thejiral/Separator-filtration_system/images/magnetholder-heatinserts-front.png

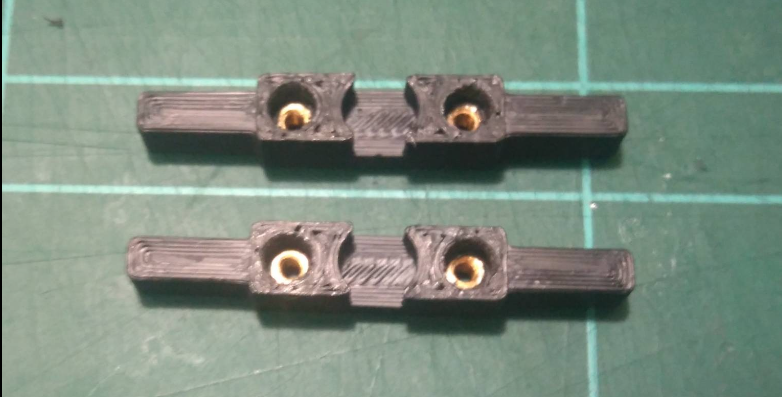
images/magnetholder-heatinserts-front.png
