thejiral/Separator-filtration_system/images/magnetholder-heatinserts.png

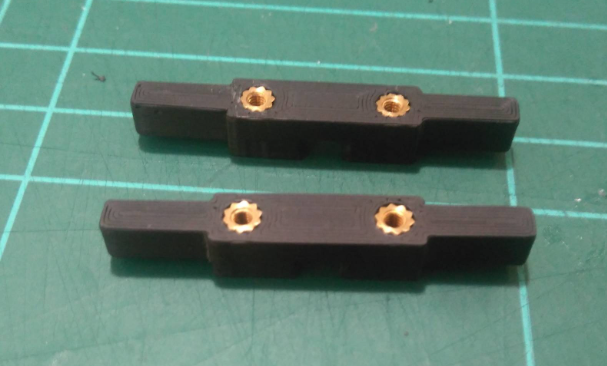
images/magnetholder-heatinserts.png
