thejiral/Separator-filtration_system/images/Meshinsert.png

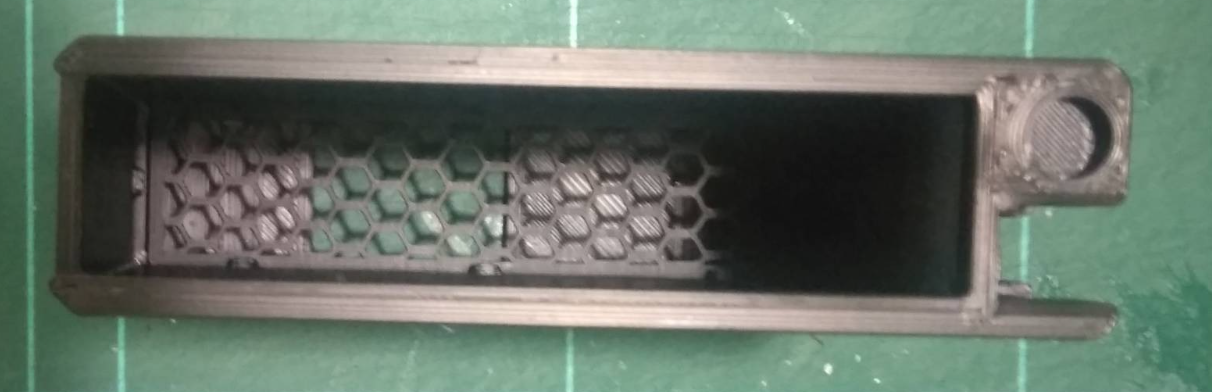
images/Meshinsert.png
