thejiral/Separator-filtration_system/images/PartA-heatinserts.png

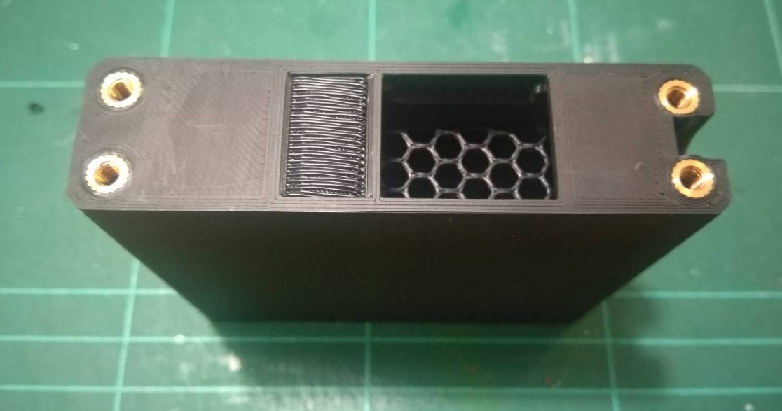
images/PartA-heatinserts.png
