thejiral/Separator-filtration_system/images/PartB-microfit_orientation.png

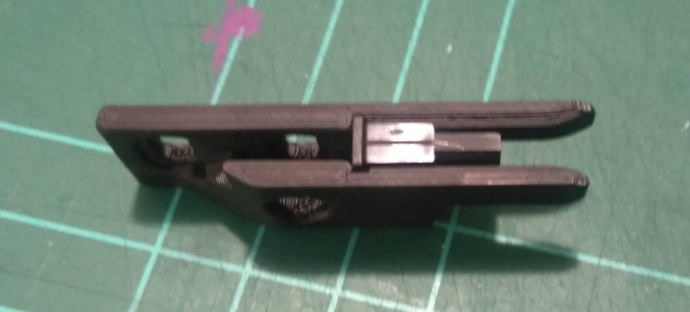
images/PartB-microfit_orientation.png
