thejiral/Separator-filtration_system/images/PartD+blower+cablemanagement.png

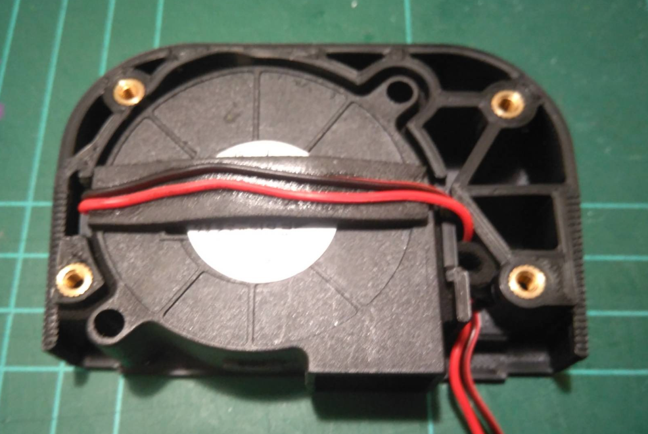
images/PartD+blower+cablemanagement.png
