thejiral/Separator-filtration_system/images/partD-heatinserts+EPDM.png

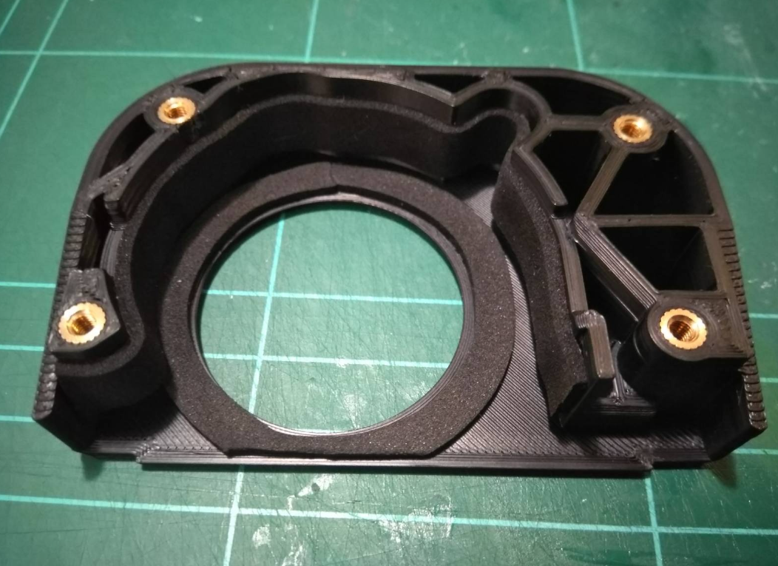
images/partD-heatinserts+EPDM.png
