thejiral/Separator-filtration_system/images/profile-magnet0.png

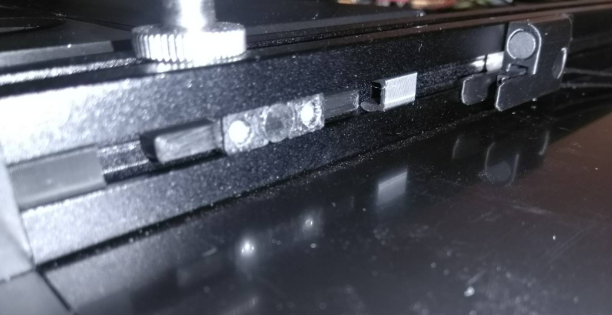
images/profile-magnet0.png
