thejiral/Separator-filtration_system/images/profile-magnet1.png

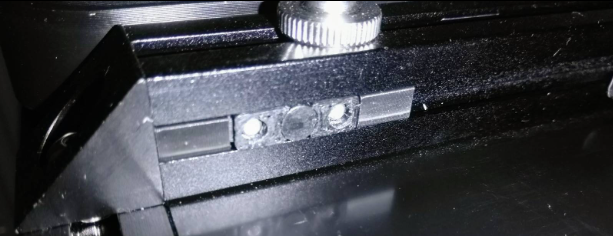
images/profile-magnet1.png
