thejiral/Separator-filtration_system/STL-dual_module/Separator-Mesh-front-modifier1.stl

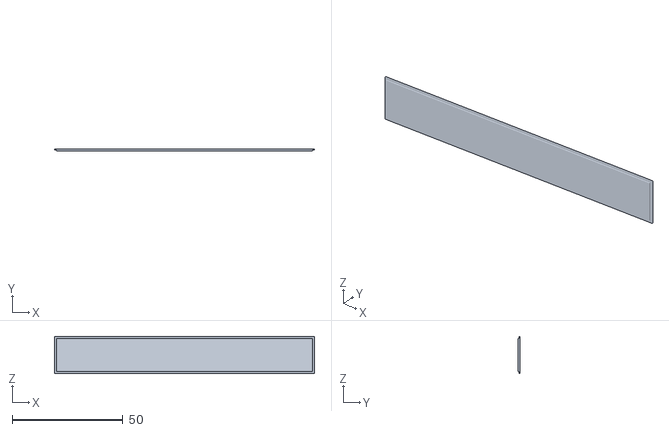
[picture p30: CAD file, 2023-09-04]
STL-dual_module/Separator-Mesh-front-modifier1.stl
117.3 x 0.8 x 16.8
