thejiral/Separator-filtration_system/STL-dual_module/profile-magnet-holderB.stl

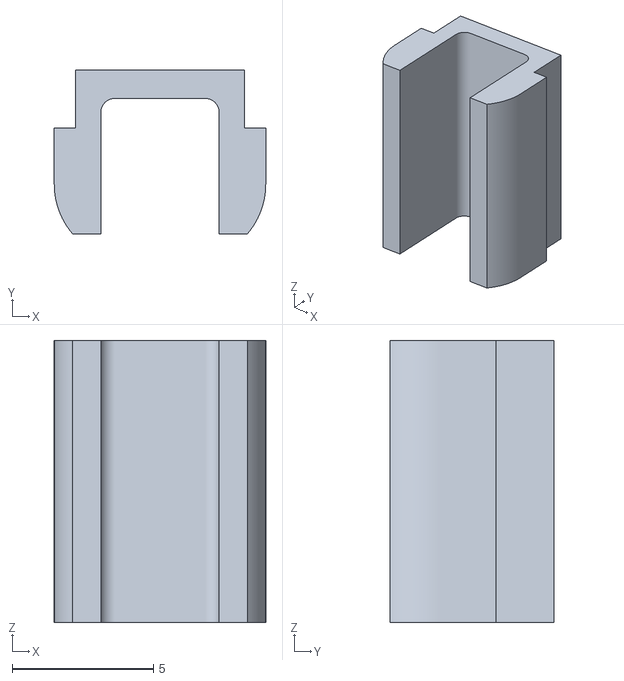
[picture p31: CAD file, 2023-09-04]
STL-dual_module/profile-magnet-holderB.stl
7.50 x 5.80 x 10.0
