thejiral/Separator-filtration_system/STL-dual_module/partC-dual.stl

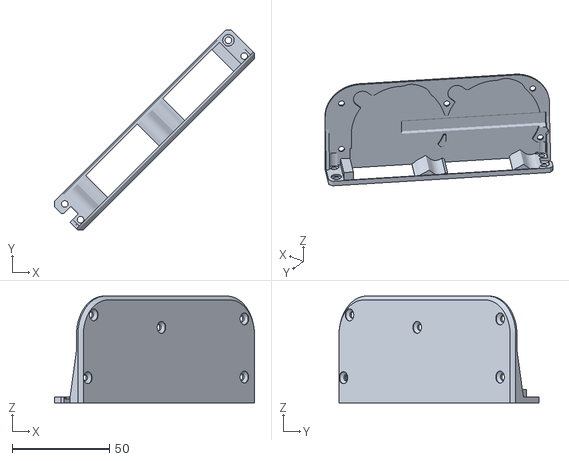
[picture p32: CAD file, 2023-09-04]
STL-dual_module/partC-dual.stl
103.0 x 103.0 x 55.0
