thejiral/Separator-filtration_system/images/Full_assembly-magnets+cablemanagement.png

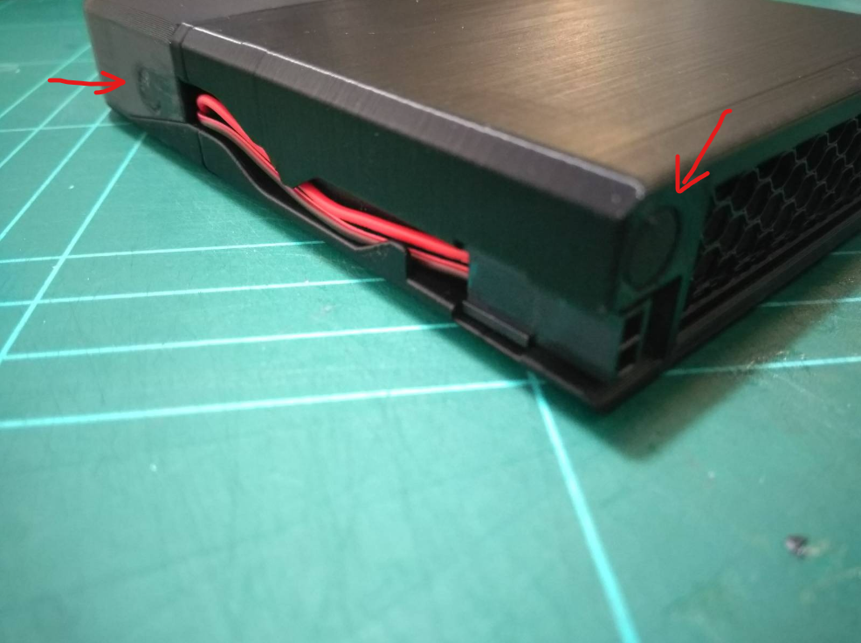
images/Full_assembly-magnets+cablemanagement.png
