thejiral/Separator-filtration_system/images/Full_installation.png

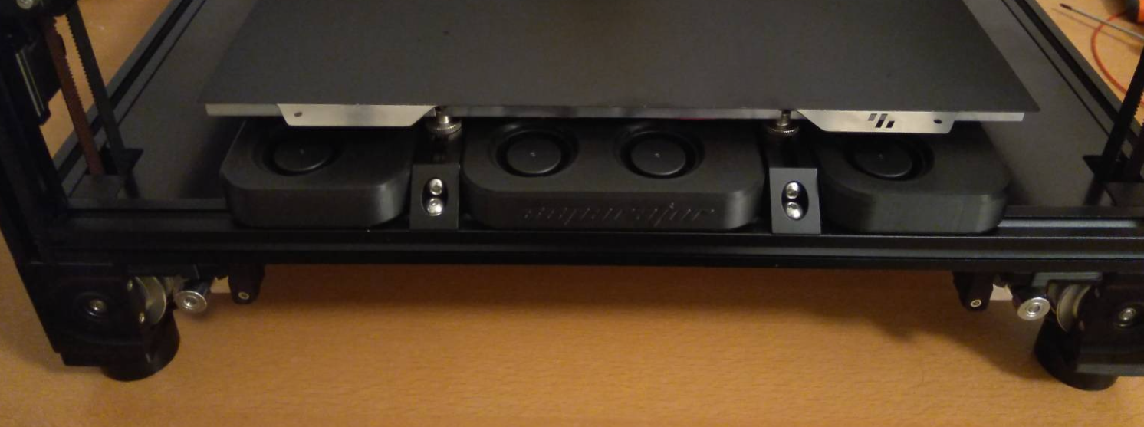
images/Full_installation.png
