thejiral/Separator-filtration_system/images/PartA+C_assembly.png

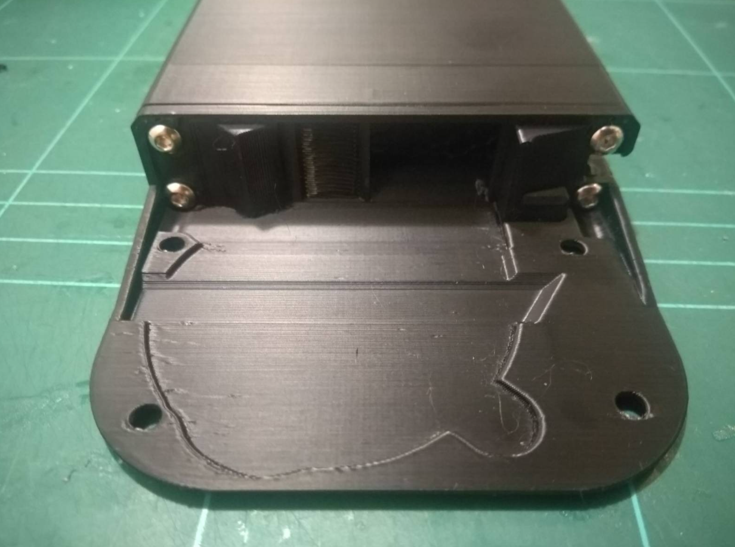
images/PartA+C_assembly.png
