thejiral/Separator-filtration_system/images/microfit-connection-testfit.png

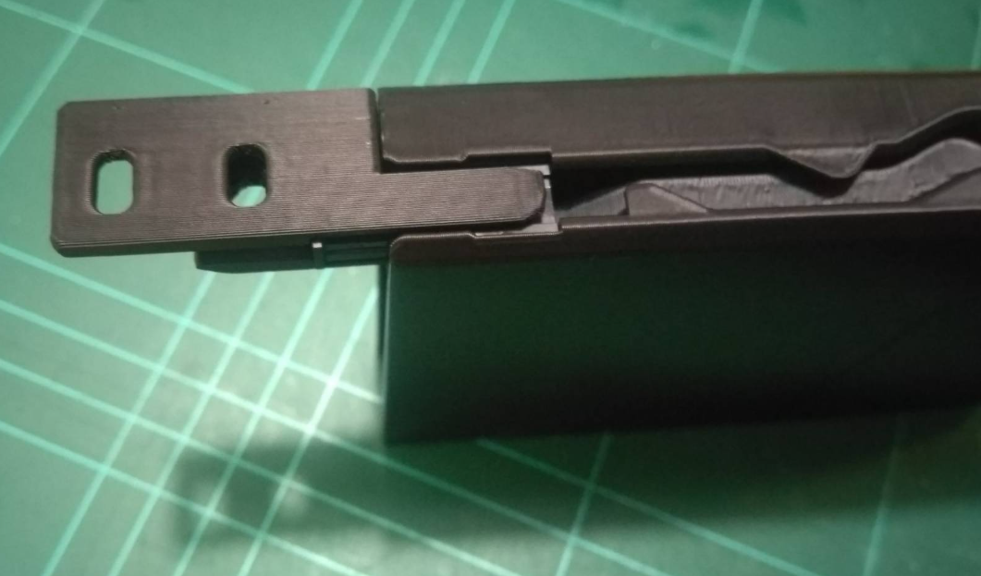
images/microfit-connection-testfit.png
